rjwalters/softstart/hardware/kicad/softstart.kicad_sch

## KiCad design hardware/kicad/softstart.kicad_sch (2026-01-20)

Schematic: softstart.kicad_sch

Parts:
C1, C2, C4, C12, C13, C14: 100nF; C_0805_2012Metric
C3: 4.7uF; C_0805_2012Metric
C5: 470pF; C_0805_2012Metric
C9, C10, C11: 10uF; C_0805_2012Metric
C101, C102, C103, C104, C105, C106, C107, C108, C109, C110, C111, C112, C113, C114, C115, C116, C117, C118, C119, C120, C121, C122, C123, C124, C125, C126, C127, C128, C129, C130, C131, C132, C133, C134, C135, C136, C137, C138, C139, C140, C141, C142, C143, C144, C145, C146, C147, C148, C149, C150, C151, C152, C153, C154, C155, C156, C157, C158, C159, C160: 12F 2.7V; CP_Radial_D10.0mm_P5.00mm
D1, D2, D3, D4: SMBJ18A; D_SMB
D6, D7: 1N4007; D_SMA
D8: Green; LED_0805_2012Metric
J1: AC_IN; TerminalBlock_Phoenix_MKDS-1,5-2_1x02_P5.00mm_Horizontal
J2: AC_OUT; TerminalBlock_Phoenix_MKDS-1,5-2_1x02_P5.00mm_Horizontal
J3: SWD; PinHeader_1x05_P2.54mm_Vertical
PS1: HLK-PM12; Converter_ACDC_Hi-Link_HLK-PMxx
Q1, Q2, Q3, Q4: IRFB4110; TO-220-3_Vertical
Q5, Q6: AO3400; SOT-23
Q7, Q8: 2N7002; SOT-23
R1, R2: 47k; R_0805_2012Metric
R3, R5, R7, R9, R14, R15, R18, R21, R22: 10k; R_0805_2012Metric
R4: 1M; R_0805_2012Metric
R6, R8: 820k; R_0805_2012Metric
R10, R11, R12, R13: 10R; R_0805_2012Metric
R16, R17: 100R 5W; R_2512_6332Metric
R19: 3.3k; R_0805_2012Metric
R20: 1k; R_0805_2012Metric
R23, R24: 220R 2W; R_2512_6332Metric
R25: 330R; R_0805_2012Metric
RV1: 275VAC; RV_Disc_D12mm_W4.2mm_P7.5mm
R_GB1, R_GB2, R_GB3, R_GB4: 10k; R_0805_2012Metric
R_SHUNT: 5mR; R_2512_6332Metric
U1: STM32G031F6P6; TSSOP-20_4.4x6.5mm_P0.65mm
U2, U3, U9, U10: UCC27511A; SOT-23-5
U4: INA180A3; SOT-23-5
U5: LMV331; SOT-23-5
U6: H11AA1; DIP-6_W7.62mm
U8: AMS1117-3.3; SOT-223-3_TabPin2
